Christian-Loja/Modular-PCB-Design-for-Seismic-Monitoring/images_PCB_3D_view/3D_1.png

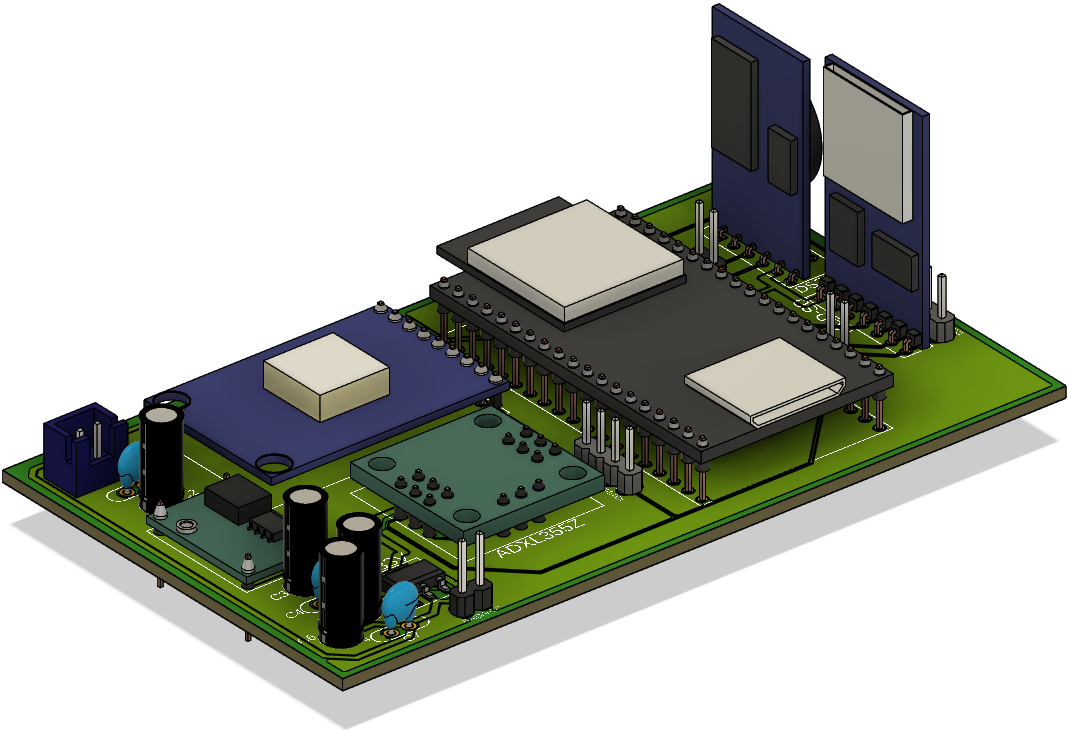
images_PCB_3D_view/3D_1.png
