Christian-Loja/Modular-PCB-Design-for-Seismic-Monitoring/images_PCB_3D_view/top_3D.png

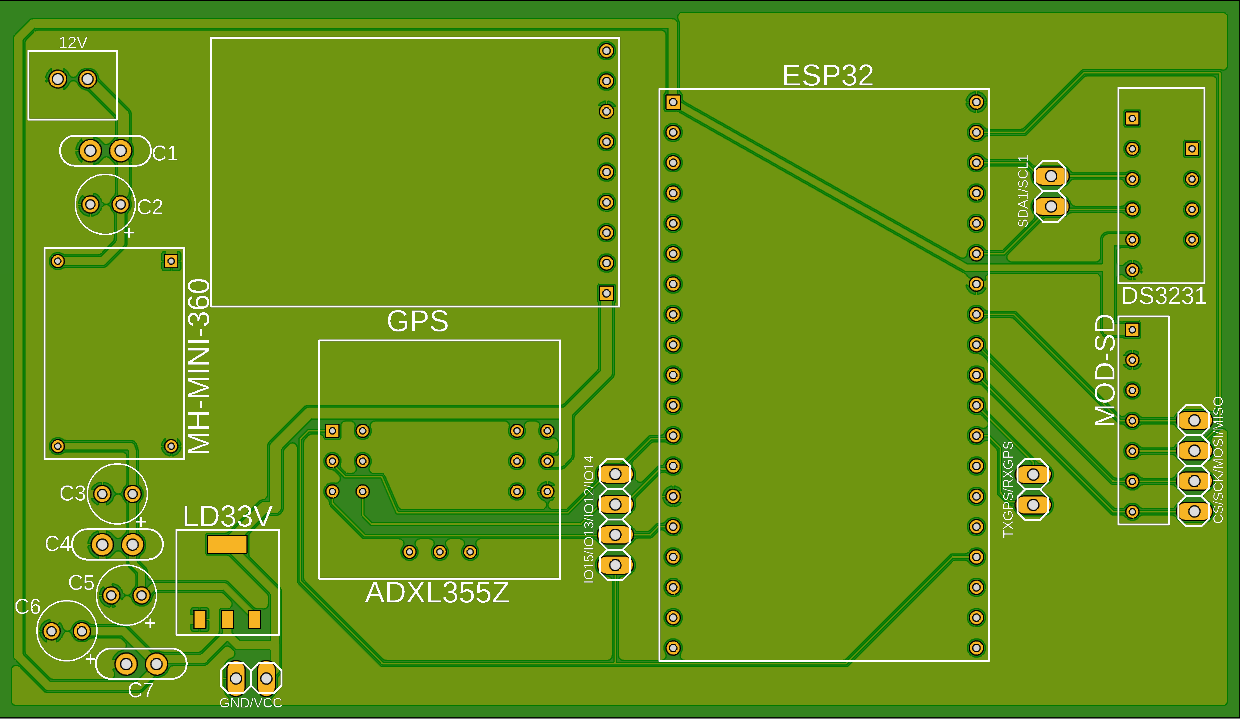
images_PCB_3D_view/top_3D.png
