Christian-Loja/Modular-PCB-Design-for-Seismic-Monitoring/images_PCB_layers/DRC.png

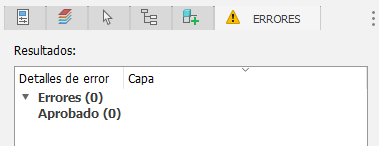
images_PCB_layers/DRC.png
