Christian-Loja/Modular-PCB-Design-for-Seismic-Monitoring/images_PCB_layers/top_bottom_route.png

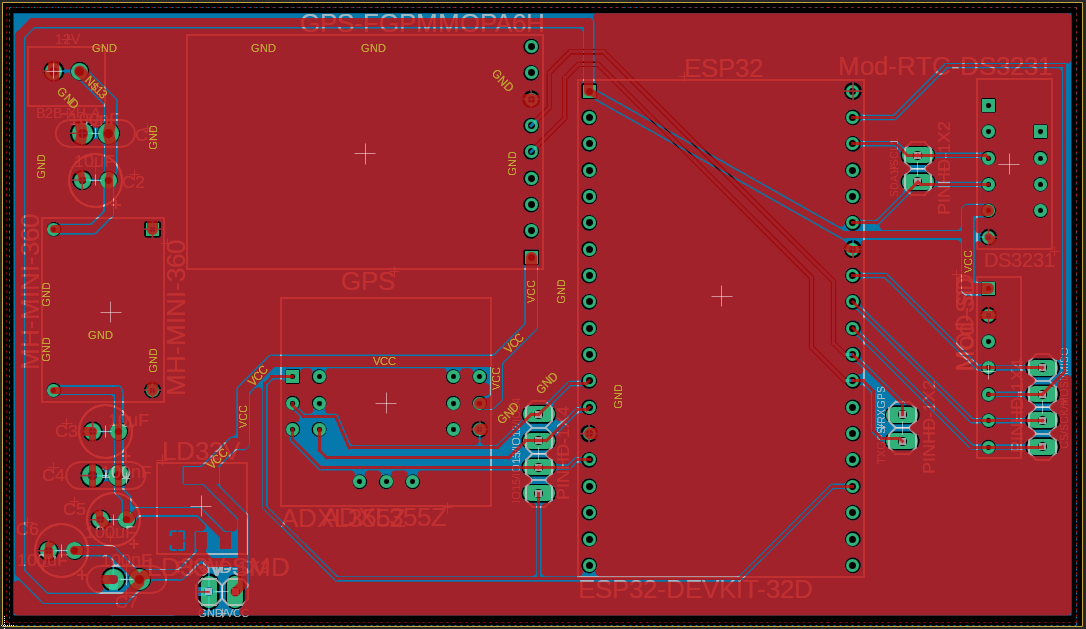
images_PCB_layers/top_bottom_route.png
