Christian-Loja/Modular-PCB-Design-for-Seismic-Monitoring/images_schematic/ERC.png

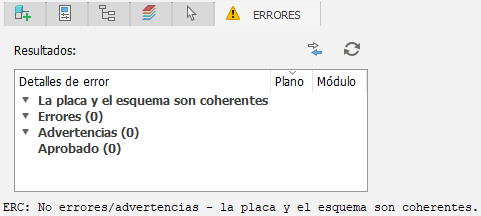
images_schematic/ERC.png
