Christian-Loja/Modular-PCB-Design-for-Seismic-Monitoring/images_schematic/schematic_5.png

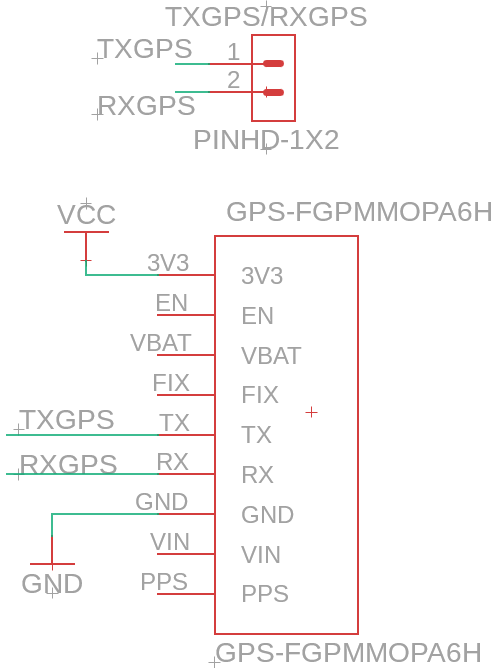
images_schematic/schematic_5.png
