Christian-Loja/Modular-PCB-Design-for-Seismic-Monitoring/images_schematic/schematic_6.png

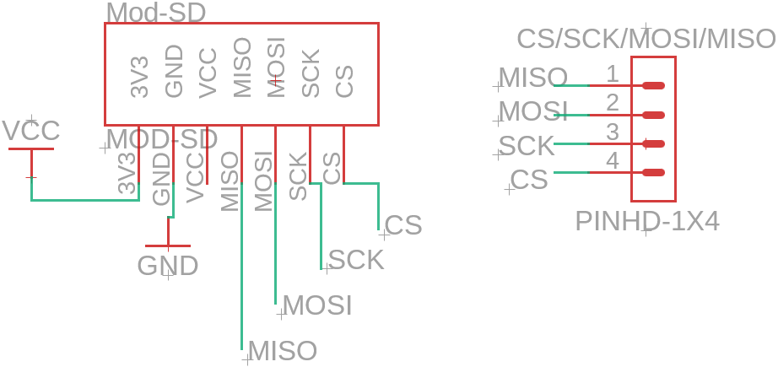
images_schematic/schematic_6.png
