Christian-Loja/Modular-PCB-Design-for-Seismic-Monitoring/images_schematic/schematic_full.png

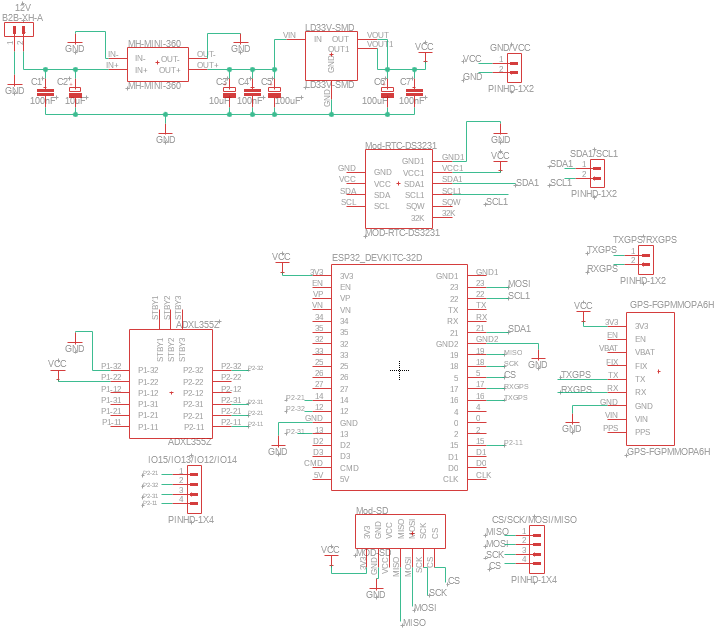
images_schematic/schematic_full.png
