Christian-Loja/Modular-PCB-Design-for-Seismic-Monitoring/images_PCB_layers/pads_components.png

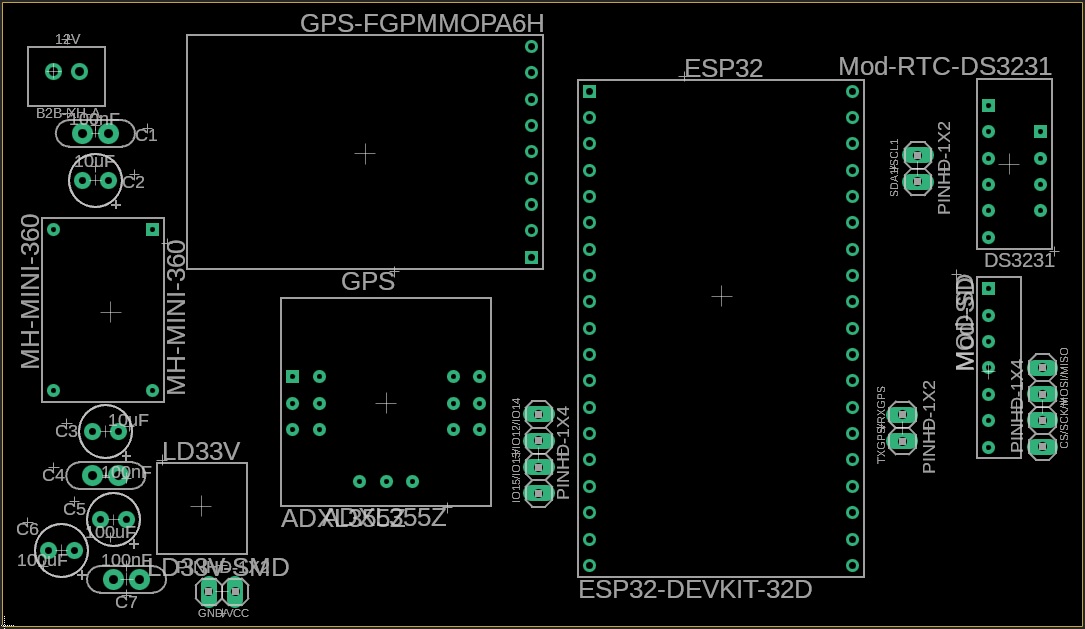
images_PCB_layers/pads_components.png
